RakshitGoel007/Multi-Rail-Power-Management-Board/results/PowerRails_Sequencing_Plot.png

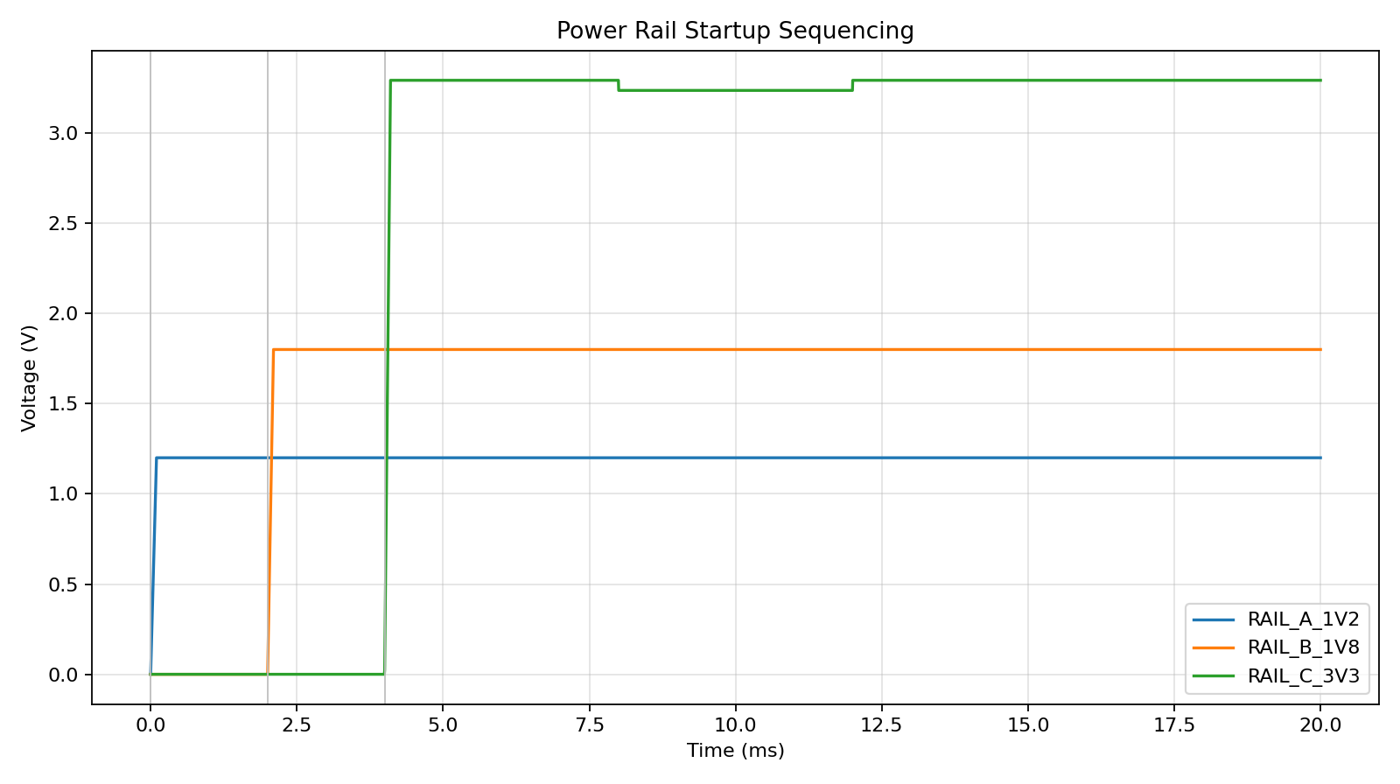
results/PowerRails_Sequencing_Plot.png
