RakshitGoel007/Multi-Rail-Power-Management-Board/results/RailC_Load_Transient_Plot.png

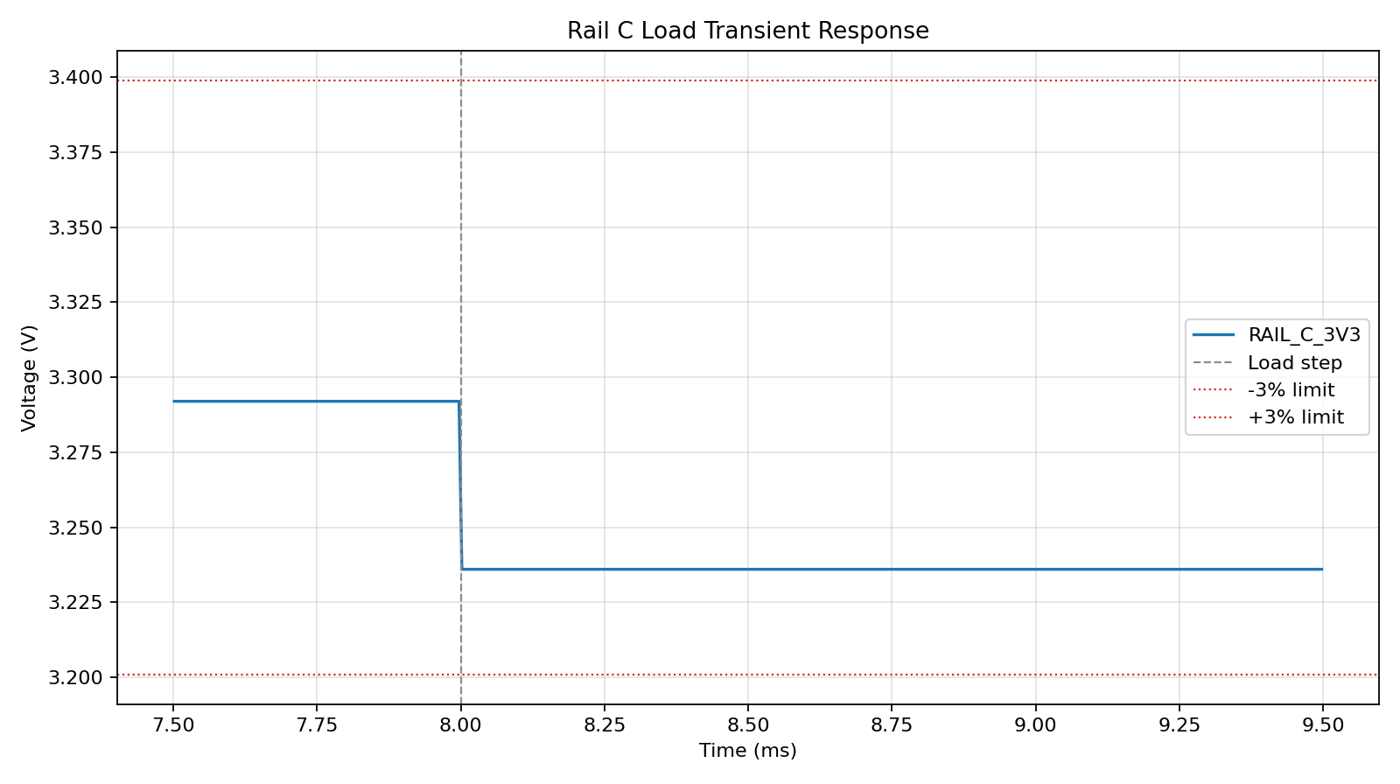
results/RailC_Load_Transient_Plot.png
