RakshitGoel007/Multi-Rail-Power-Management-Board/ltspice/PowerRails_Behavioral_Complete.asc

BRAIL_A: bv; V=RA(time)
BRAIL_B: bv; V=RB(time)
BRAIL_C: bv; V=RC(time)
CAOUT: cap; 22µ
CBOUT: cap; 22µ
CCOUT: cap; 22µ
IC_LOADSTEP: current; I=LOAD(time)
RLOADA: res; 2.4
RLOADB: res; 3
RLOADC_LIGHT: res; 33
VEN_A: bv; V=ENA(time)
VEN_B: bv; V=ENB(time)
VEN_C: bv; V=ENC(time)
VINPUT: voltage; 5
Named nets: VIN_5V, 0, RAIL_A_1V2, RAIL_B_1V8, RAIL_C_3V3, EN_A, EN_B, EN_C
Multi-Rail Power Management Board - LTspice Sequencing Simulation
Plot: V(RAIL_A_1V2), V(RAIL_B_1V8), V(RAIL_C_3V3), V(EN_A), V(EN_B), V(EN_C)
5 V input
Rail A: 1.2 V core, tON = 0 ms
Rail B: 1.8 V I/O, tON = 2 ms
Rail C: 3.3 V sensors, tON = 4 ms
Enable timing monitor signals
Simulation directives
.func RA(t) if(t>=0,1.2,0)
.func RB(t) if(t>=2m,1.8,0)
.func RC(t) if(t>=4m,3.292,0)-if(t>=8m,if(t<12m,56m,0),0)
.func LOAD(t) if(t>=8m,if(t<12m,0.7,0),0)
.func ENA(t) if(t>=0,5,0)
.func ENB(t) if(t>=2m,5,0)
.func ENC(t) if(t>=4m,5,0)
.tran 20m startup
.save V(VIN_5V) V(EN_A) V(EN_B) V(EN_C) V(RAIL_A_1V2) V(RAIL_B_1V8) V(RAIL_C_3V3) I(IC_LOADSTEP)
Measurements
.meas tran RailA_90pct_time WHEN V(RAIL_A_1V2)=1.08 RISE=1
.meas tran RailB_90pct_time WHEN V(RAIL_B_1V8)=1.62 RISE=1
.meas tran RailC_90pct_time WHEN V(RAIL_C_3V3)=2.97 RISE=1
.meas tran RailC_pre_step_avg AVG V(RAIL_C_3V3) FROM=7m TO=7.8m
.meas tran RailC_load_step_min MIN V(RAIL_C_3V3) FROM=8m TO=9m
.meas tran RailC_recovered_avg AVG V(RAIL_C_3V3) FROM=9m TO=12m
