RakshitGoel007/Multi-Rail-Power-Management-Board/ltspice/PowerRails_REAL.asc

U1: TPS62203
U2: TPS62240_TRANS
U3: TLV70012
V1: voltage; 5
Named nets: 0, VIN_5V
Open this file from the clean folder: Desktop/Rail_LTspice_Project
.lib TPS62203.lib
.lib TPS62240_TRANS.lib
.lib TLV70012.lib
.tran 10m startup
U1 TPS62203: 3.3 V buck
U2 TPS62240: 1.8 V buck
U3 TLV70012: 1.2 V LDO
