RakshitGoel007/Multi-Rail-Power-Management-Board/kicad/PowerRailsBoard_KiCad/PowerRailsBoard.kicad_sch

## KiCad design kicad/PowerRailsBoard_KiCad/PowerRailsBoard.kicad_sch (2026-07-26)

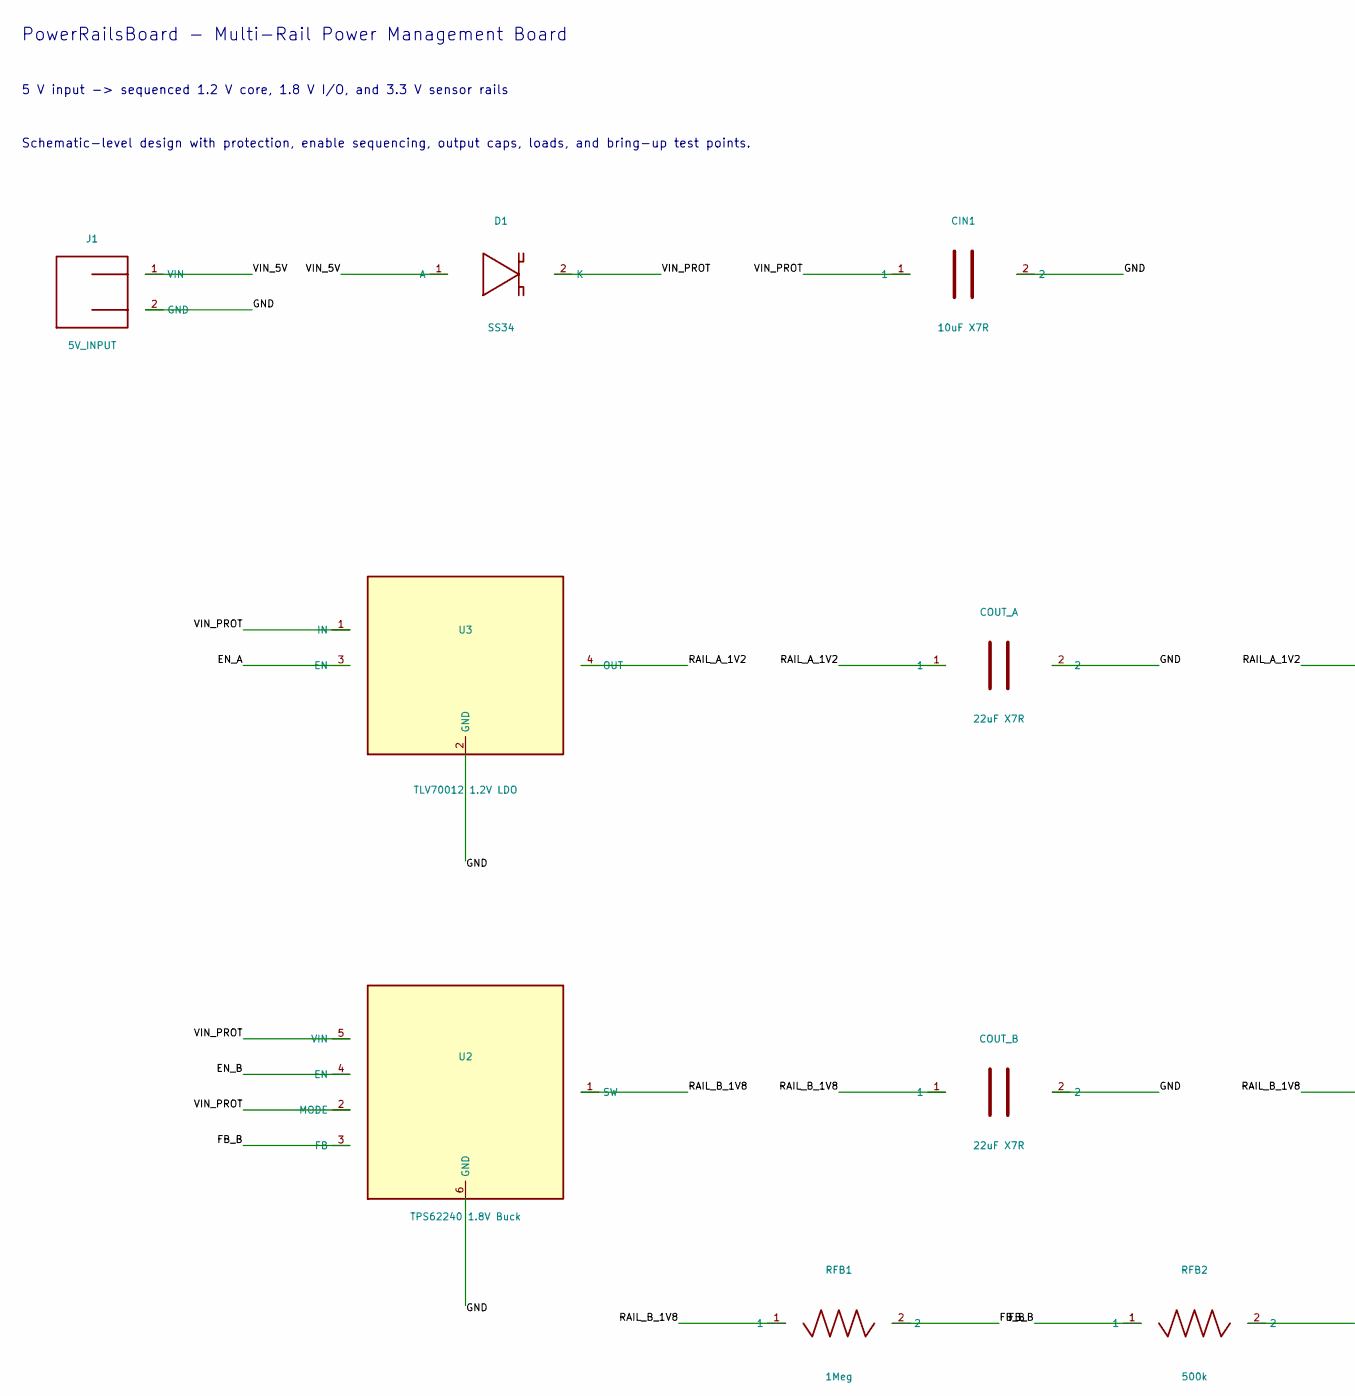
[picture p5: schematic PowerRailsBoard.kicad_sch, part in row 1, column 1]

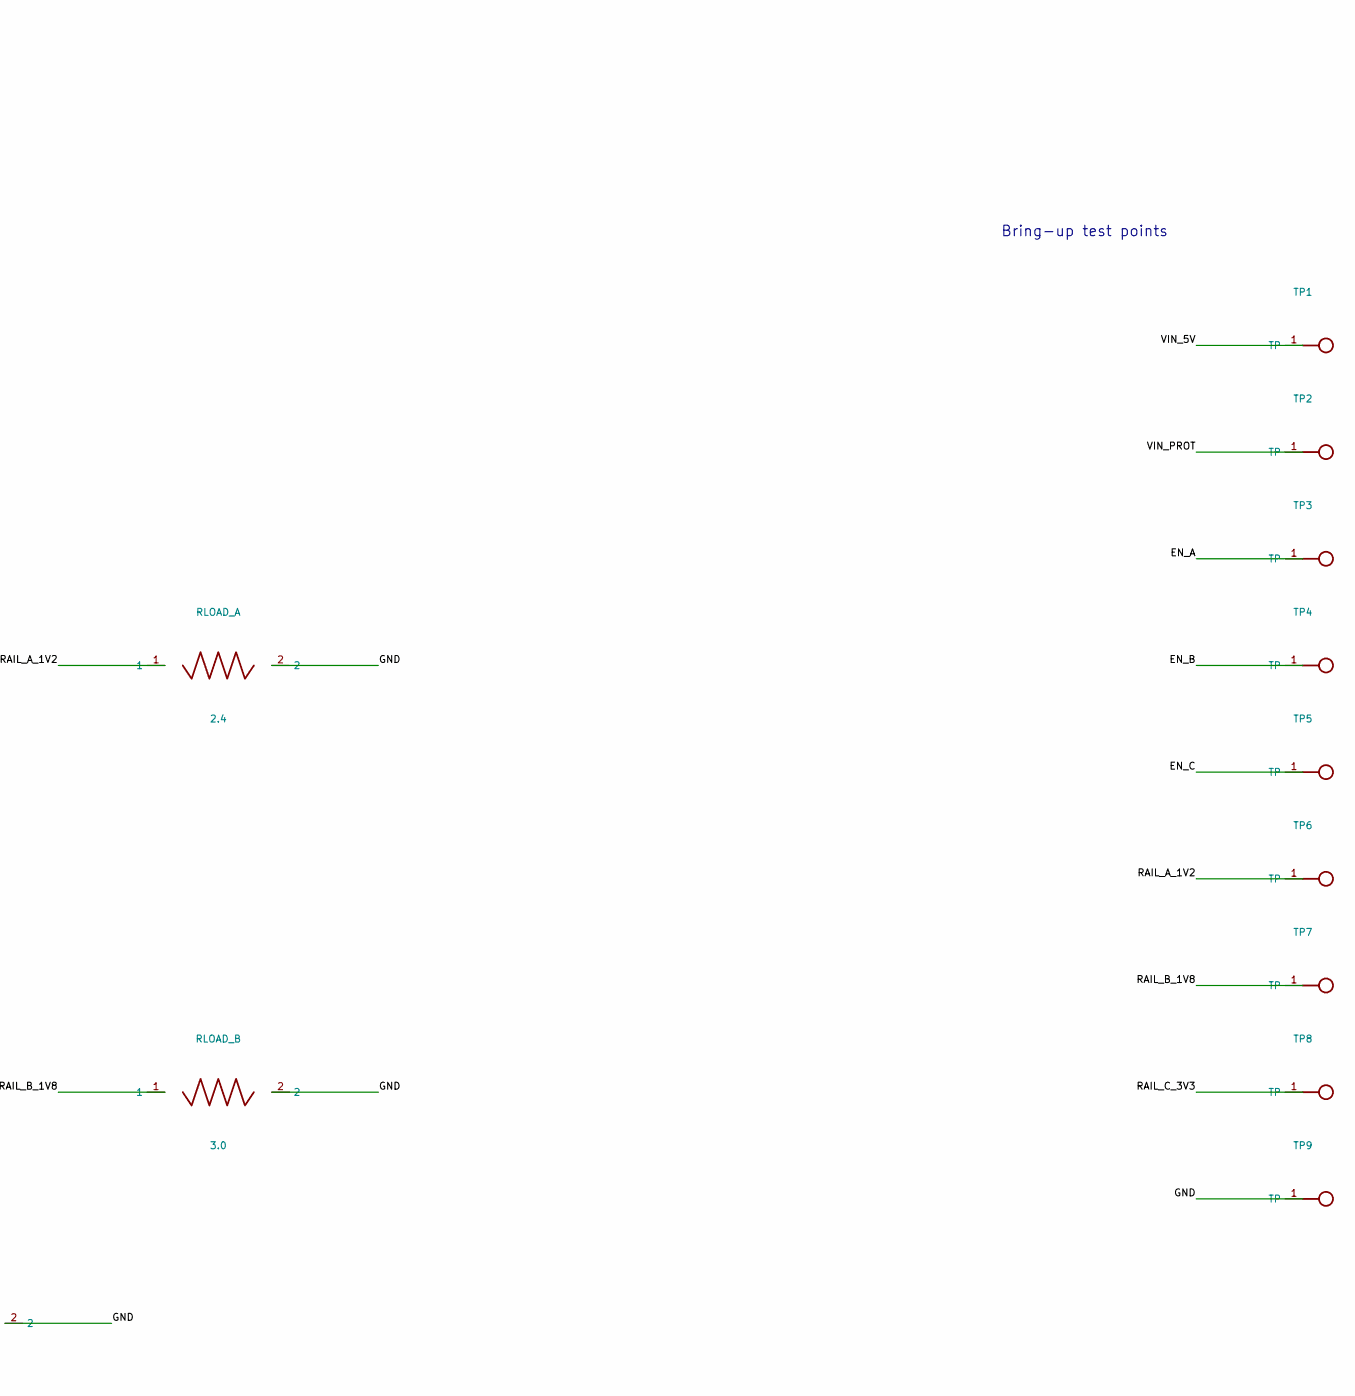
[picture p6: schematic PowerRailsBoard.kicad_sch, part in row 1, column 2]

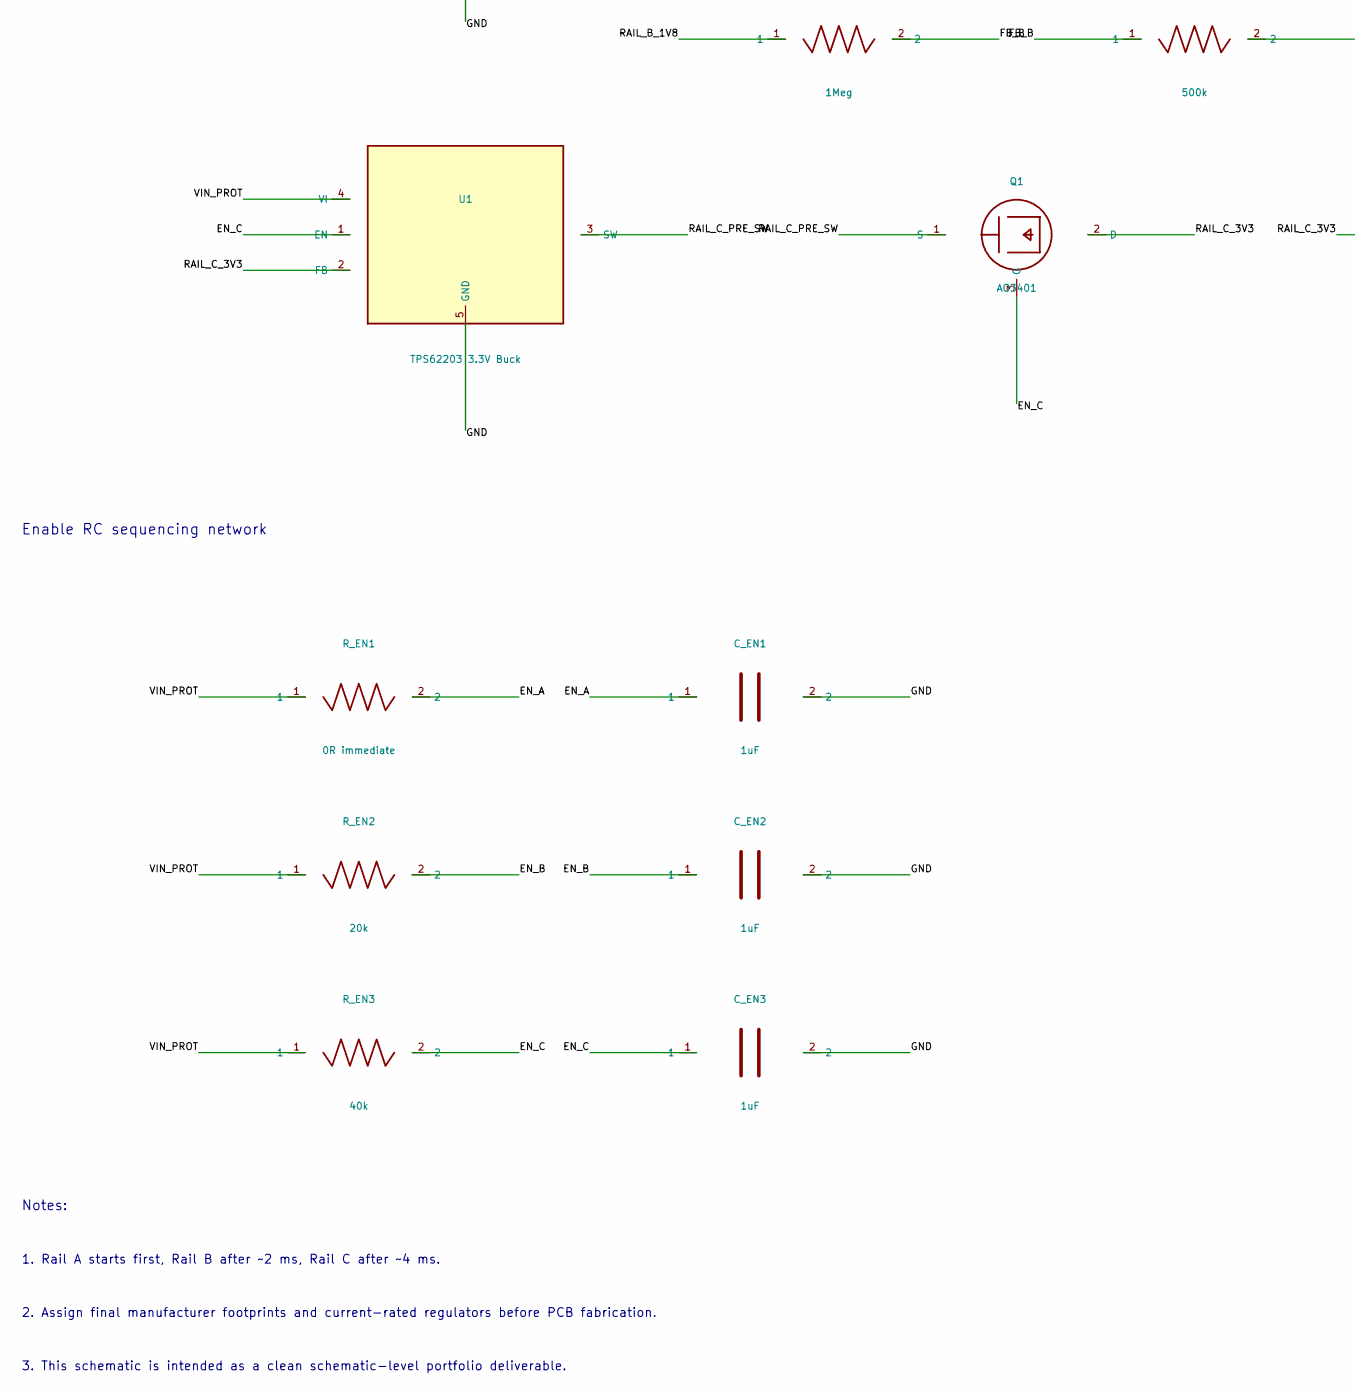
[picture p7: schematic PowerRailsBoard.kicad_sch, part in row 2, column 1]

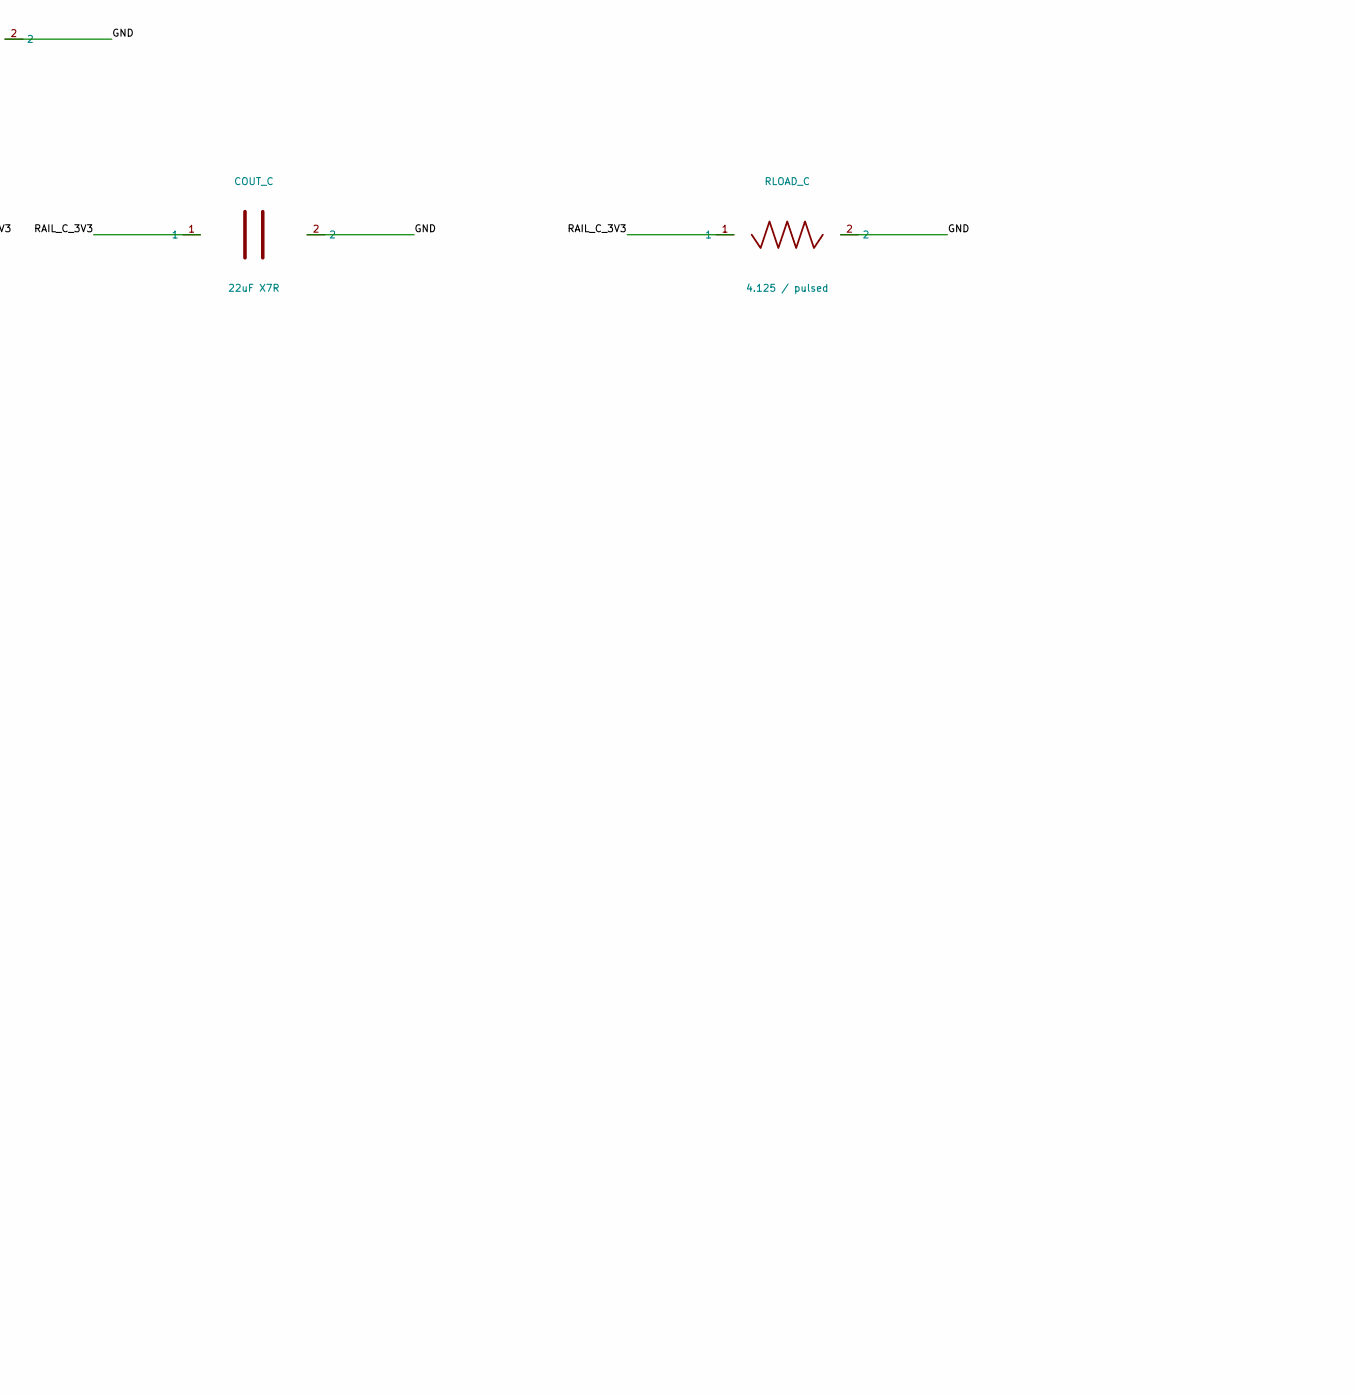
[picture p8: schematic PowerRailsBoard.kicad_sch, part in row 2, column 2]

Parts:
CIN1: 10uF X7R; C_0805_2012Metric
COUT_A: 22uF X7R; C_0805_2012Metric
COUT_B: 22uF X7R; C_0805_2012Metric
COUT_C: 22uF X7R; C_0805_2012Metric
C_EN1, C_EN2, C_EN3: 1uF; C_0805_2012Metric
D1: SS34; D_SMA
J1: 5V_INPUT; PinHeader_1x02_P2.54mm_Vertical
Q1: AO3401; SOT-23
RFB1: 1Meg; R_0603_1608Metric
RFB2: 500k; R_0603_1608Metric
RLOAD_A: 2.4; R_0603_1608Metric
RLOAD_B: 3.0; R_0603_1608Metric
RLOAD_C: 4.125 / pulsed; R_0603_1608Metric
R_EN1: 0R immediate; R_0603_1608Metric
R_EN2: 20k; R_0603_1608Metric
R_EN3: 40k; R_0603_1608Metric
TP1: VIN_5V; TestPoint_Pad_D1.5mm
TP2: VIN_PROT; TestPoint_Pad_D1.5mm
TP3: EN_A; TestPoint_Pad_D1.5mm
TP4: EN_B; TestPoint_Pad_D1.5mm
TP5: EN_C; TestPoint_Pad_D1.5mm
TP6: RAIL_A_1V2; TestPoint_Pad_D1.5mm
TP7: RAIL_B_1V8; TestPoint_Pad_D1.5mm
TP8: RAIL_C_3V3; TestPoint_Pad_D1.5mm
TP9: GND; TestPoint_Pad_D1.5mm
U1: TPS62203 3.3V Buck; SOT-23-5
U2: TPS62240 1.8V Buck; SOT-23-5
U3: TLV70012 1.2V LDO; SOT-23-5

Connections:
EN_A: C_EN1.1, R_EN1.2, TP3.1, U3.3 (EN)
EN_B: C_EN2.1, R_EN2.2, TP4.1, U2.4 (EN)
EN_C: C_EN3.1, Q1.3 (G), R_EN3.2, TP5.1, U1.1 (EN)
FB_B: RFB1.2, RFB2.1, U2.3 (FB)
GND: CIN1.2, COUT_A.2, COUT_B.2, COUT_C.2, C_EN1.2, C_EN2.2, C_EN3.2, J1.2 (GND), RFB2.2, RLOAD_A.2, RLOAD_B.2, RLOAD_C.2, TP9.1, U1.5 (GND), U2.6 (GND), U3.2 (GND)
RAIL_A_1V2: COUT_A.1, RLOAD_A.1, TP6.1, U3.4 (OUT)
RAIL_B_1V8: COUT_B.1, RFB1.1, RLOAD_B.1, TP7.1, U2.1 (SW)
RAIL_C_3V3: COUT_C.1, Q1.2 (D), RLOAD_C.1, TP8.1, U1.2 (FB)
RAIL_C_PRE_SW: Q1.1 (S), U1.3 (SW)
VIN_5V: D1.1 (A), J1.1 (VIN), TP1.1
VIN_PROT: CIN1.1, D1.2 (K), R_EN1.1, R_EN2.1, R_EN3.1, TP2.1, U1.4 (VI), U2.2 (MODE), U2.5 (VIN), U3.1 (IN)

Notes on the sheet:
PowerRailsBoard - Multi-Rail Power Management Board
5 V input -> sequenced 1.2 V core, 1.8 V I/O, and 3.3 V sensor rails
Schematic-level design with protection, enable sequencing, output caps, loads, and bring-up test points.
Enable RC sequencing network
Bring-up test points
Notes:
1. Rail A starts first, Rail B after ~2 ms, Rail C after ~4 ms.
2. Assign final manufacturer footprints and current-rated regulators before PCB fabrication.
3. This schematic is intended as a clean schematic-level portfolio deliverable.
